b-Tomas/enclosed-media-vault/CAD/case/demo/case-built-front-closeup.jpg

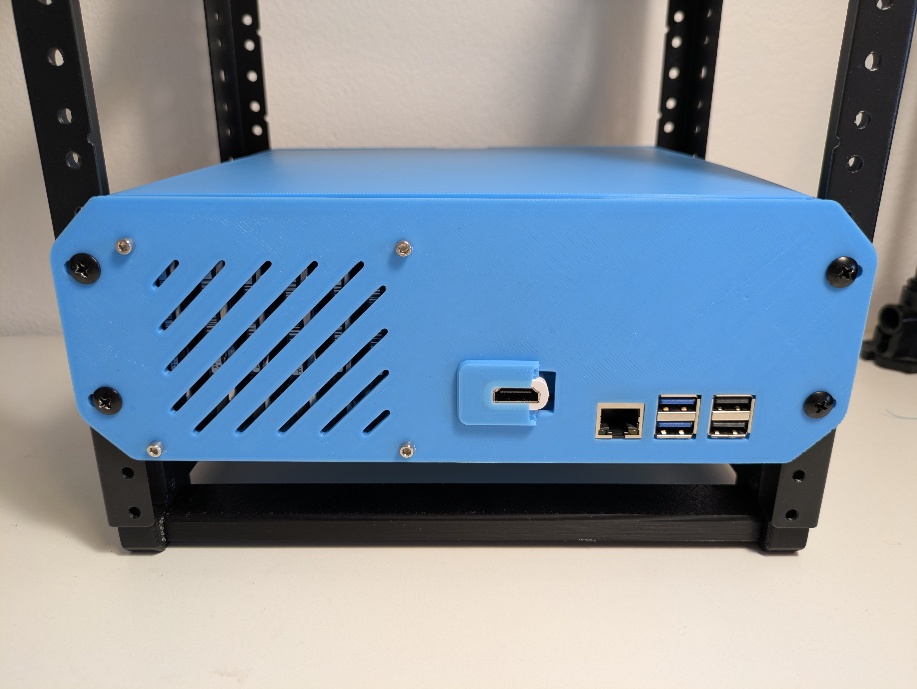
CAD/case/demo/case-built-front-closeup.jpg
