b-Tomas/enclosed-media-vault/CAD/case/demo/case-no-cover.jpg

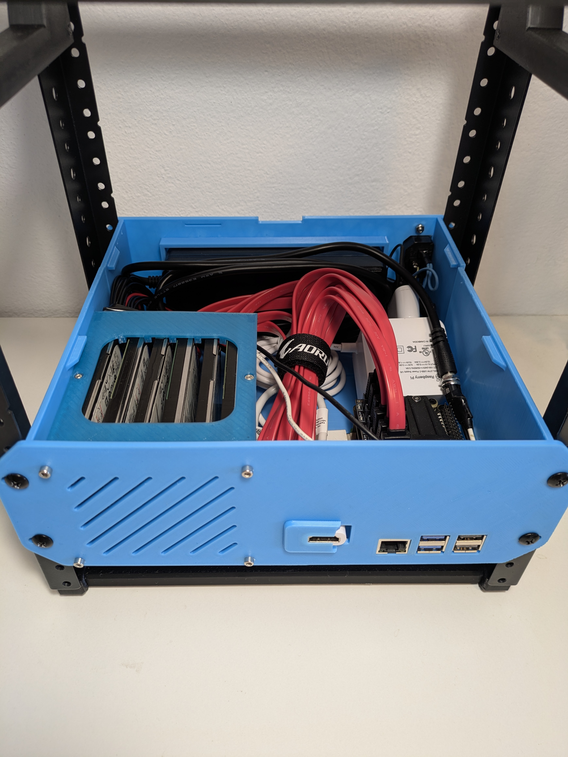
CAD/case/demo/case-no-cover.jpg
