b-Tomas/enclosed-media-vault/CAD/base-chassis/demo/base-examples-printed.jpg

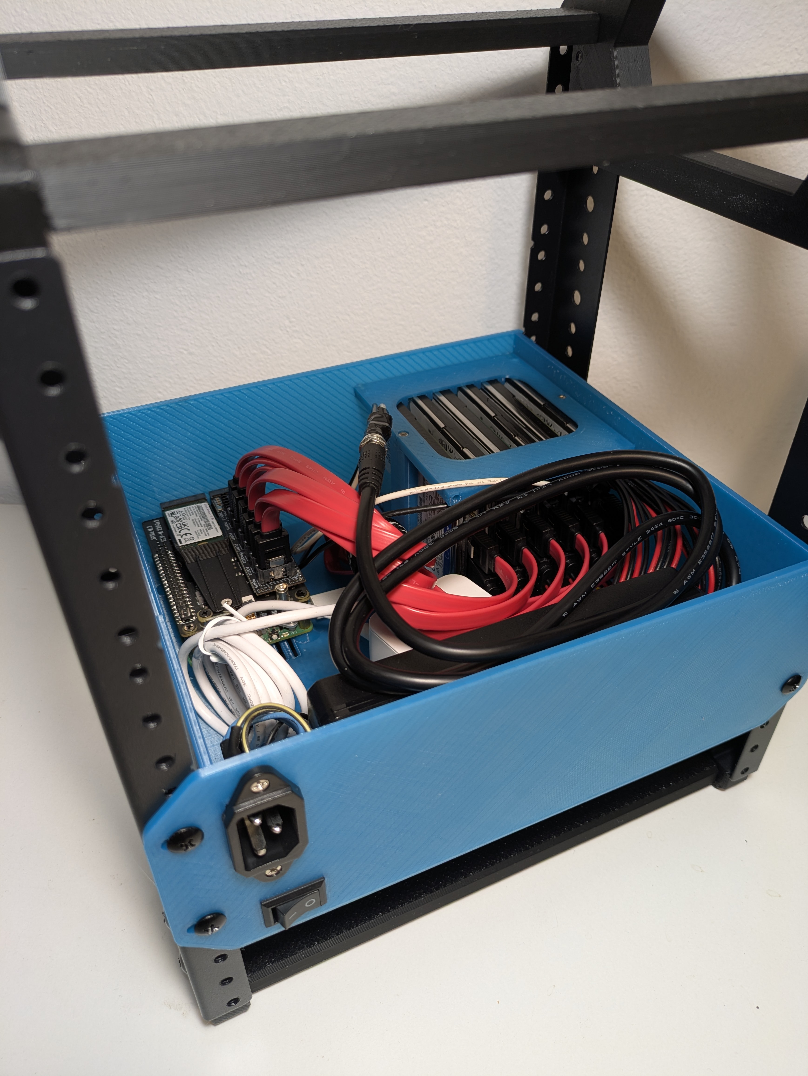
CAD/base-chassis/demo/base-examples-printed.jpg
