b-Tomas/enclosed-media-vault/CAD/drives/demo/drives-usage-1.jpg

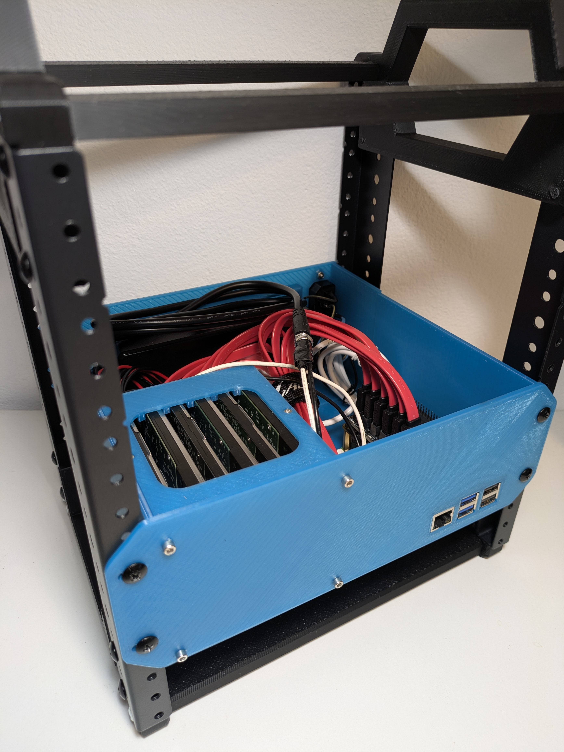
CAD/drives/demo/drives-usage-1.jpg
