b-Tomas/enclosed-media-vault/CAD/drives/demo/drives-usage-2.jpg

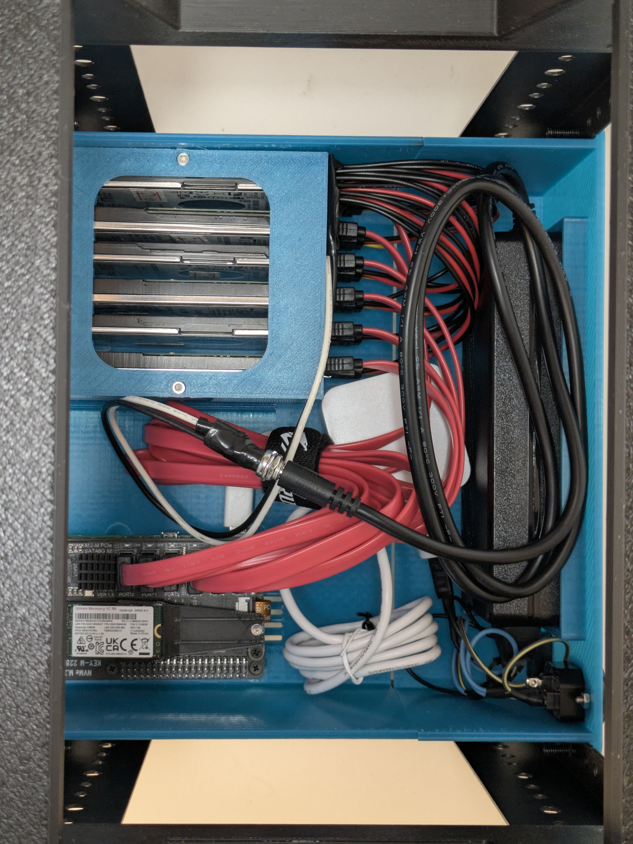
CAD/drives/demo/drives-usage-2.jpg
